r315/psu/f103/Inc/main.h

#define VOUT_Pin GPIO_PIN_0
#define VOUT_GPIO_Port GPIOA
#define IOUT_Pin GPIO_PIN_1
#define IOUT_GPIO_Port GPIOA
#define ILOAD_Pin GPIO_PIN_2
#define ILOAD_GPIO_Port GPIOA
#define VLOAD_Pin GPIO_PIN_3
#define VLOAD_GPIO_Port GPIOA
#define DBG_Pin GPIO_PIN_4
#define DBG_GPIO_Port GPIOA
#define T2_Pin GPIO_PIN_13
#define T2_GPIO_Port GPIOB
#define TT_Pin GPIO_PIN_14
#define TT_GPIO_Port GPIOB
#define T1_Pin GPIO_PIN_15
#define T1_GPIO_Port GPIOB
