r315/psu/App/draw.c

#include "board.h"
#include "draw.h"

volatile uint8_t lcd_busy = 0;
static uint16_t _color;
// use dual buffer for speed
static uint16_t _scratch[2][SCRATCH_BUF_SIZE];
static uint8_t bufidx = 0;
uint16_t *scratch = _scratch[0];

/**
 * Called from DMA end of transfer interrupt
 * */
void spi_eot(void){
    LCD_CS1;
    lcd_busy = 0;
}

/**
 * @brief Draws bitmap on display, data has format {w,h,data...}
 * 
 * @param x : x position
 * @param y : y position
 * @param data : bitmap data
 */
void DRAW_Bitmap(uint16_t x, uint16_t y, uint16_t *data){
    DRAW_Tile(x, y, data+2, data[0], data[1]);
}

/**
 * @brief Draws tile, blocking if the last transfer not finished.
 * other access lcd access should be avoided .
 * 
 * @param x : x position
 * @param y : y position
 * @param data : tile data, usually the scratch pointer 
 * @param w : tile width
 * @param h : tile height
 */
void DRAW_Tile(uint16_t x, uint16_t y, uint16_t *data, uint16_t w, uint16_t h){
    while(lcd_busy);
    lcd_busy = 1;
    LCD_Window(x, y, w, h);
    LCD_CS0;
    SPI_WriteDMA(data, w * h);
    // swap buffer    
    scratch = _scratch[(++bufidx) & 1];
}

/**
 * @brief draw filled rectangle
 * */
void DRAW_FillRect(uint16_t x, uint16_t y,  uint16_t w, uint16_t h, uint16_t color){
    while(lcd_busy);
    lcd_busy = 1;
    LCD_Window(x, y, w, h);
    LCD_CS0;
    _color = color;
	SPI_WriteDMA(&_color, (w * h) | 0x80000000);
}

/**
 * @brief draw vertical line
 * 
 * @param x,y : start x,y position
 * @param h : line hight
 * @param color : line color
 * */
void DRAW_VLine(uint16_t x, uint16_t y, uint16_t h, uint16_t color){
    DRAW_FillRect(x, y, 1, h, color);
}

/**
 * @brief draw horizontal line
 * 
 * @param x,y : start x,y position
 * @param h : line width
 * @param color : line color
 * */
void DRAW_HLine(uint16_t x, uint16_t y, uint16_t w, uint16_t color){
    DRAW_FillRect(x, y, w, 1, color);
}

/**
 * @brief 
 * 
 * @param x,y : start x,y position
 * @param h : line width
 * @param color : line color
 * */
void DRAW_Pixel(uint16_t x, uint16_t y, uint16_t color){
    while(lcd_busy);
    LCD_Pixel(x, y, color);
}

/**
 * @brief Converts an 1bpp icon to single 16bit color bitmap.
 * Note: icon data should be left aligned
 * 
 * @param bitmap : pointer to bitmap output
 * @param icon : input icon, data format {w,h,data...}
 * @param fcolor : forecolor 16bit color
 * @param bcolor : backgroundcolor 16bit color
 * */
void DRAW_Icon2Bitmap(uint16_t *bitmap, uint8_t *icon, uint16_t fcolor, uint16_t bcolor){
    uint16_t w, h;

    w = *icon++;
    h = *icon++;

    *bitmap++ = w;
    *bitmap++ = h;

    for(uint8_t i = 0; i < h; i++, icon++){
        uint8_t bmap = *icon;
        uint8_t mask = 0x80;
        for(uint8_t j = 0; j < w; j++, mask >>= 1, bitmap++){
            if(mask == 0){
                mask = 0x80;
                bmap = *(++icon);
            }
            if(bmap & mask) *bitmap = fcolor;
            else *bitmap = bcolor;
        }
    }
}

/**
 * @brief Draws 1bpp icon with BLACK background
 * 
 * @param x : x position on display
 * @param y : y position on display
 * @param icon : input icon, data format {w,h,data...}
 * @param color : forecolor
 * */
void DRAW_Icon(uint16_t x, uint16_t y, uint8_t *ico, uint16_t color){
    DRAW_Icon2Bitmap(scratch, ico, color, BLACK);
    DRAW_Bitmap(x, y, scratch);
}

/**
 * @brief Draws 1bpp icon
 * 
 * @param x : x position on display
 * @param y : y position on display
 * @param icon : input icon, data format {w,h,data...}
 * @param fcolor : forecolor
 * @param bcolor : backgroundcolor
 * */
void DRAW_Icon2(uint16_t x, uint16_t y, uint8_t *ico, uint16_t fcolor, uint16_t bcolor){
    DRAW_Icon2Bitmap(scratch, ico, fcolor, bcolor);
    DRAW_Bitmap(x, y, scratch);
}
