r315/psu/App/console/cmdadc.cpp

#include "psu.h"
#include "cmdadc.h"
#include "cmdutil.h"

char *getOptValue(const char *opt, uint32_t argc, char **argv);

void CmdAdc::help(void){ 
    console->print("\nUsage: adc <command>\n");
    console->print("Adc configuration\n\n");
    console->print("Commands:\n");
    console->print("\tres\t\tADC Resolution\n");
    console->print("\tcal\t\tCalibrate ADC\n");
    console->print("\tread <ch|all>\tread channel [0-15] value\n");
    console->print("\tplot <ch>\tprint channel value for graph plot\n");
    console->print("\t\tch : 0-15, 16 prints channels 0,1 for I/V plot \n");
    console->print("\tgain <ch> [float]\tget/set channel gain\n");
}

void CmdAdc::printResolution(void){
    console->print("Resolution: %.2fmv\n", ADC_GetResolution());
}

void CmdAdc::printCalibrationData(void){
    console->print("Calibration data: %u\n", ADC_GetCalibration());
}

void CmdAdc::printChannelVoltage(uint8_t channel){
    if(channel < AN_MUX_NUM_CH){
        console->print("CH %u:\t%umv\n", channel, psu_getChannelVoltage(channel));
    }
}

char CmdAdc::execute(void *ptr){ 
char *str = (char*)ptr;
int32_t intvalue;
double floatvalue;
    
    if(isNextWord(&str, "res")){
        printResolution();
        return CMD_OK;
    }

    if(isNextWord(&str, "cal")){
        ADC_Calibrate();
        printCalibrationData();        
        return CMD_OK;
    }

    if(isNextWord(&str, "read")){
        if(nextInt(&str, &intvalue)){
            printChannelVoltage(intvalue);
            return CMD_OK;
        }

        if(isNextWord(&str, "all")){
            for (size_t i = 0; i < AN_MUX_NUM_CH; i++){
                printChannelVoltage(i);
            }
            return CMD_OK;
        }
    }

    if(isNextWord(&str, "plot")){
        if(nextInt(&str, &intvalue)){
            static TickType_t xLastWakeTime;
            while( !console->kbhit() ){
                uint32_t count = g_mgr_eoc_count;
                if(intvalue < 16){
                    console->print("%d\r", psu_getChannelVoltage(intvalue));
                }else{
                    console->print("%d,%d\r", psu_getChannelVoltage(0), psu_getChannelVoltage(1));
                }
                while(count == g_mgr_eoc_count){
                    vTaskDelayUntil( &xLastWakeTime, pdMS_TO_TICKS(50));
                }
            }
            return CMD_OK;
        }
    }

    if(isNextWord(&str, "gain")){
        if(nextInt(&str, &intvalue)){
            if(nextDouble(&str, &floatvalue)){
                psu_setChannelGain(intvalue, floatvalue);
            }else{
                console->print("%.2f\n", psu_getChannelGain(intvalue));
            }
            return CMD_OK;
        }
    }

    help();
    printCalibrationData();
    printResolution();

    return CMD_BAD_PARAM;
}
