r315/psu/App/console/cmddfu.h

#ifndef _cmd_dfu_h_
#define _cmd_dfu_h_


#ifdef __cplusplus
extern "C" {
#endif

#ifdef ENABLE_DFU
#include <console.h>

//dfu-util -a 0 -s 0x08001000 -D ../build/psu_v3.bin -R

#define ENABLE_DFU_MAGIC *(((uint64_t*)&_estack) - 1) = 0xDEADBEEFCC00FFEEULL
#define DISABLE_DFU_MAGIC *(((uint64_t*)&_estack) - 1) = 0x0UL

extern uint32_t _estack;

class CmdDfu : public ConsoleCommand{
    Console *console;
public:
    void init(void *params) { DISABLE_DFU_MAGIC; console = static_cast<Console*>(params); }
    CmdDfu () : ConsoleCommand("dfu") { }
    char execute(void *ptr);
    void help(void);
};

#endif

#ifdef __cplusplus
}
#endif

#endif
