r315/psu/App/components/pcf8574.c

#include <stdint.h>
#include "board.h"

void EXPANDER_Init(void){
    // I/Os should be high before being used as inputs.
    uint8_t data = 0xFF;    
    I2C_Write(PCF8574_I2C_ADDRESS, &data, 1);
}

uint8_t EXPANDER_Read(void){
uint8_t data;
    I2C_Read(PCF8574_I2C_ADDRESS, &data, 1);
    return data;
}

void EXPANDER_Write(uint8_t data){
    I2C_Write(PCF8574_I2C_ADDRESS, &data, 1);
}
